Anti-AliasLabs/low-animal-spirit/Set Up Instructions.pages/Data/pasted-image-31.png

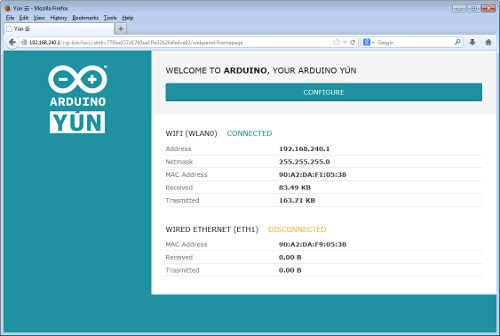
Set Up Instructions.pages/Data/pasted-image-31.png
