Anti-AliasLabs/low-animal-spirit/Set Up Instructions.pages/Data/aal-alpha-small-40.png

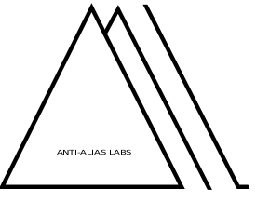
Set Up Instructions.pages/Data/aal-alpha-small-40.png
