Anti-AliasLabs/low-animal-spirit/Set Up Instructions.pages/Data/pasted-image-25.png

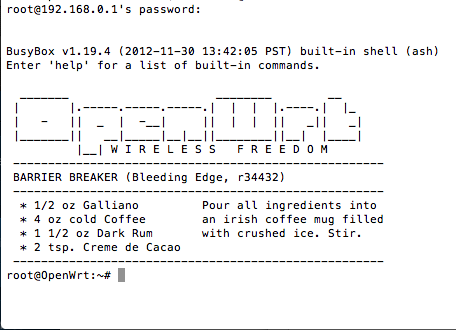
Set Up Instructions.pages/Data/pasted-image-25.png
