Anti-AliasLabs/low-animal-spirit/Set Up Instructions.pages/Data/pasted-image-34.png

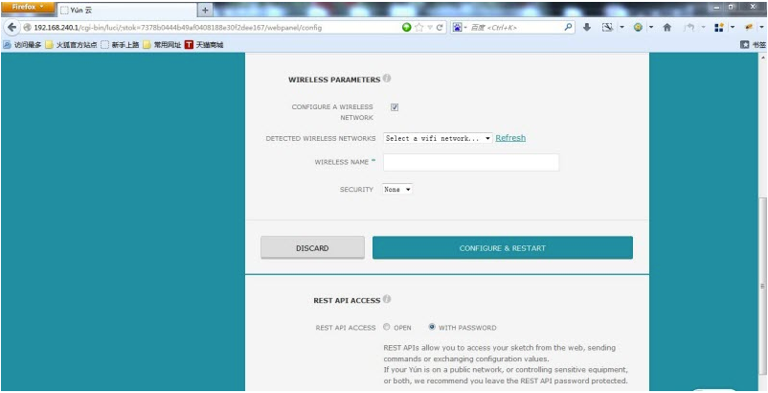
Set Up Instructions.pages/Data/pasted-image-34.png
