Anti-AliasLabs/low-animal-spirit/Set Up Instructions.pages/Data/pasted-image-small-20.png

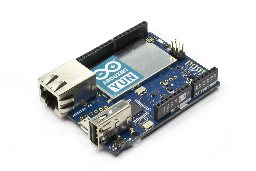
Set Up Instructions.pages/Data/pasted-image-small-20.png
