Anti-AliasLabs/low-animal-spirit/Set Up Instructions.pages/Data/pasted-image-small-26.png

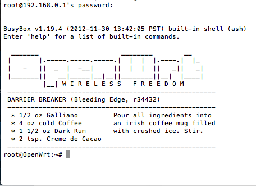
Set Up Instructions.pages/Data/pasted-image-small-26.png
